michiganaerospace/Eco-Kit/weather ui mac/humidity.png

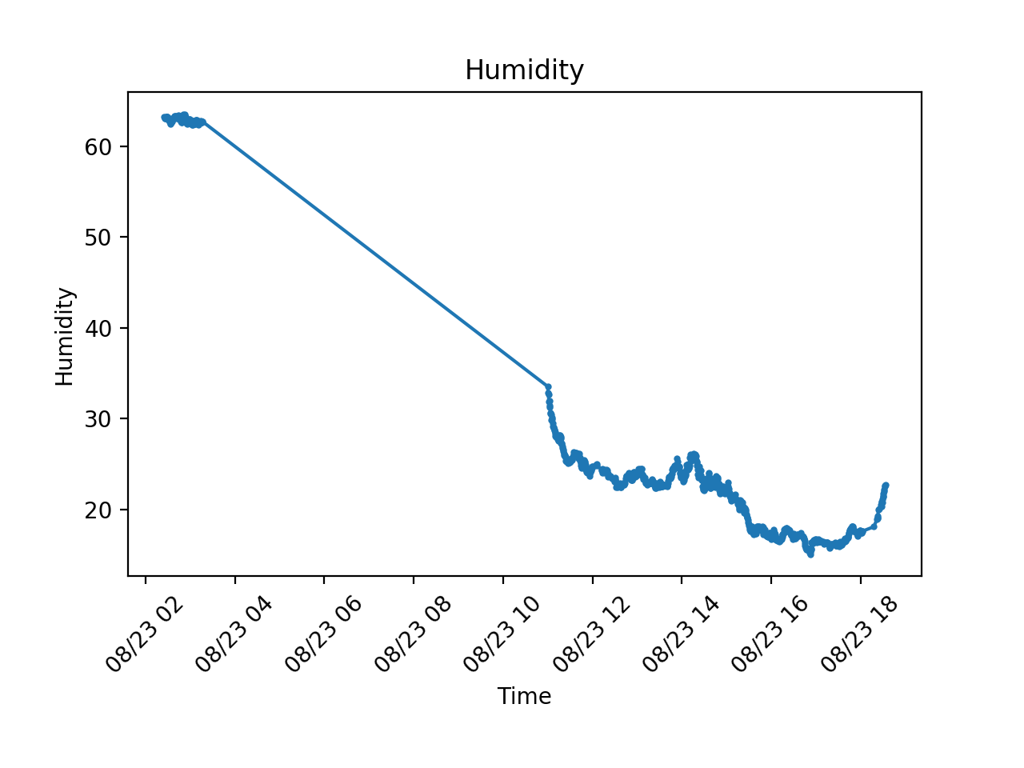
weather ui mac/humidity.png
