michiganaerospace/Eco-Kit/weather ui mac/no data.png

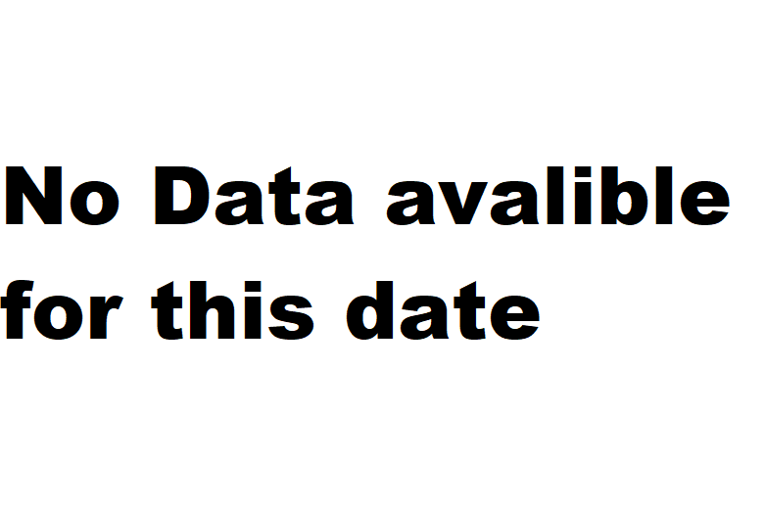
weather ui mac/no data.png
