michiganaerospace/Eco-Kit/weather ui mac/pressure.png

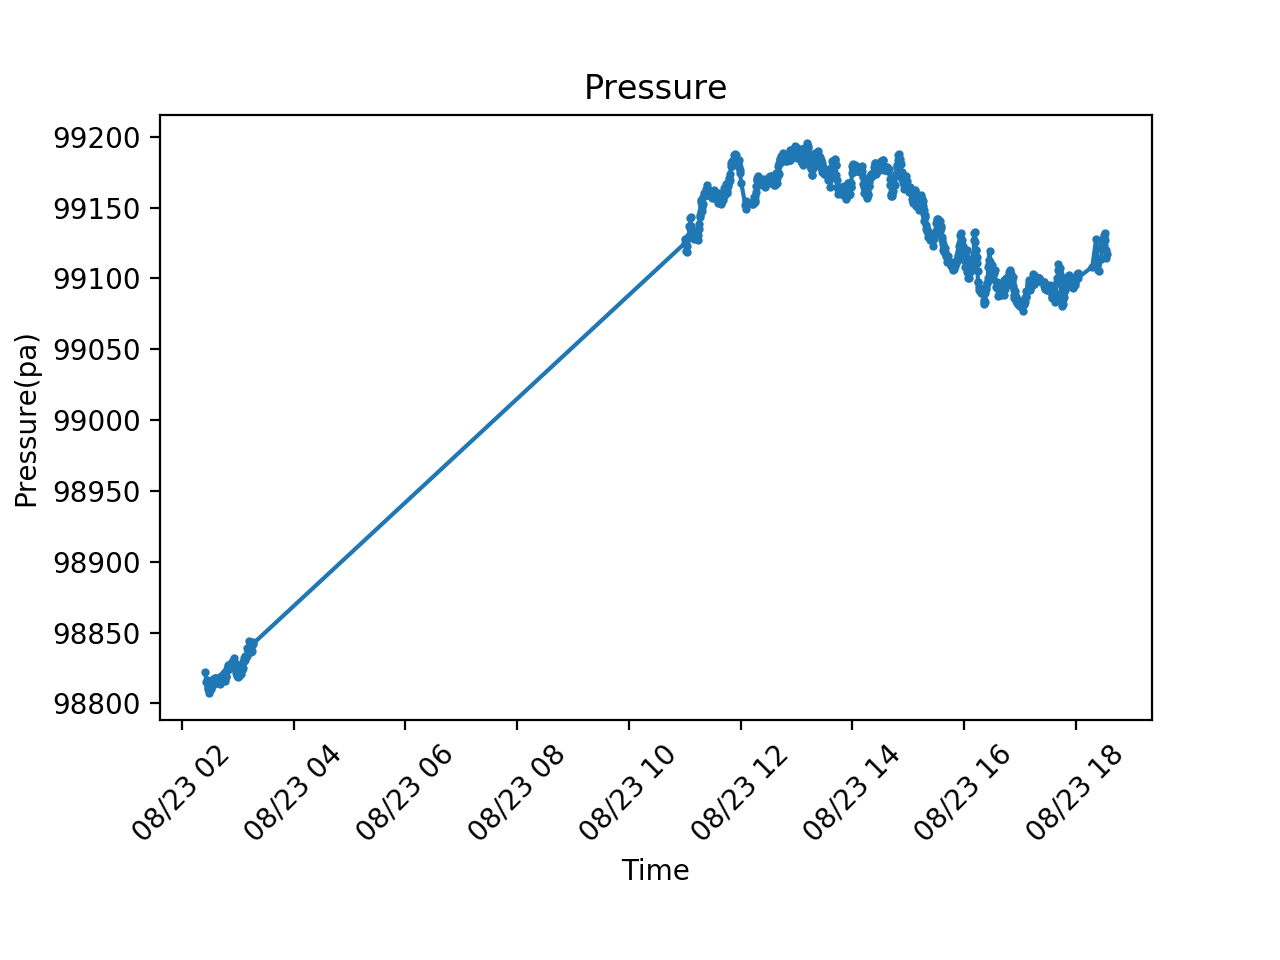
weather ui mac/pressure.png
