michiganaerospace/Eco-Kit/weather ui mac/temp.png

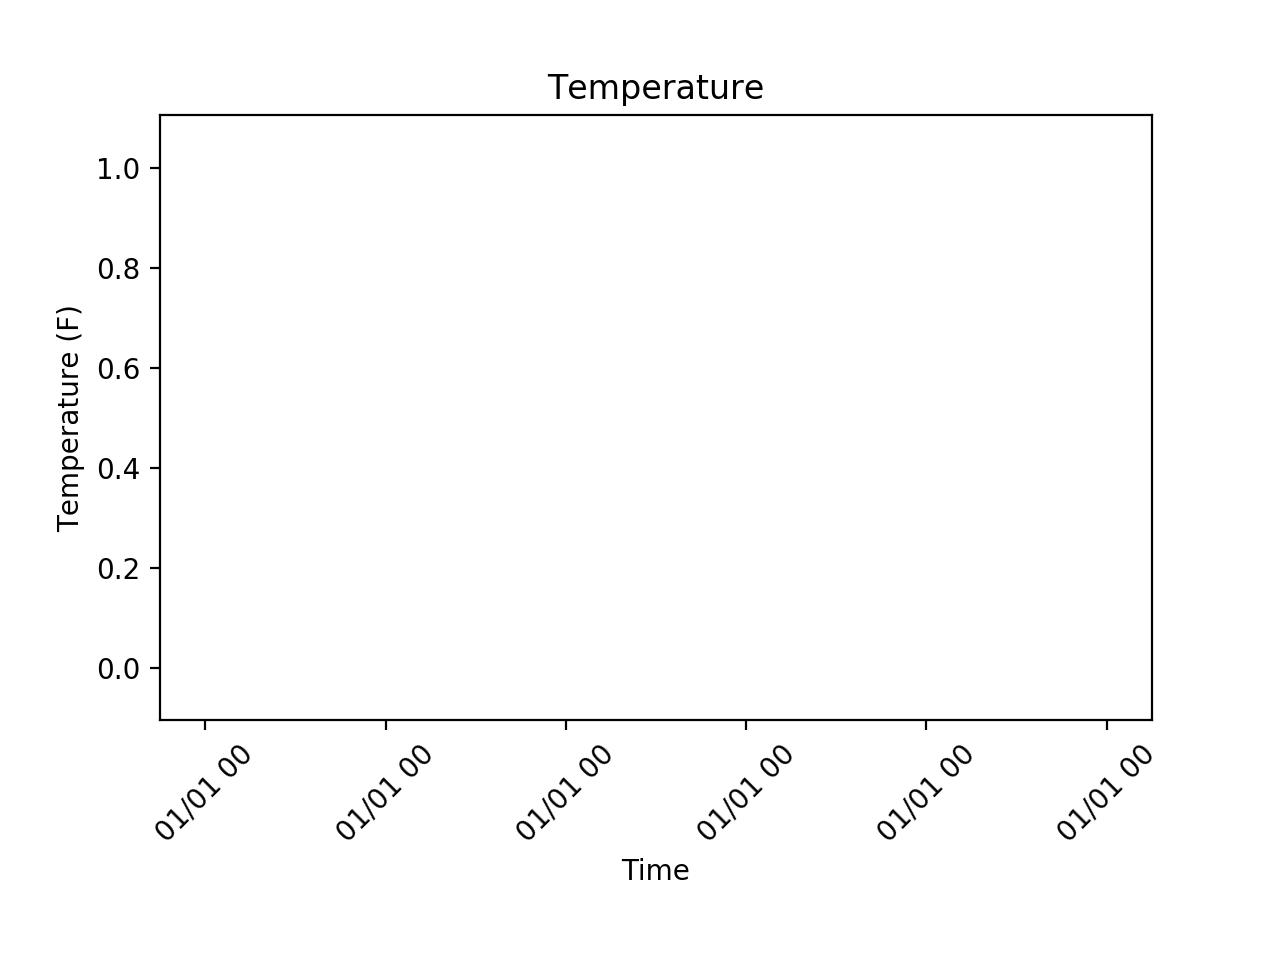
weather ui mac/temp.png
