michiganaerospace/Eco-Kit/weather ui mac/voltage.png

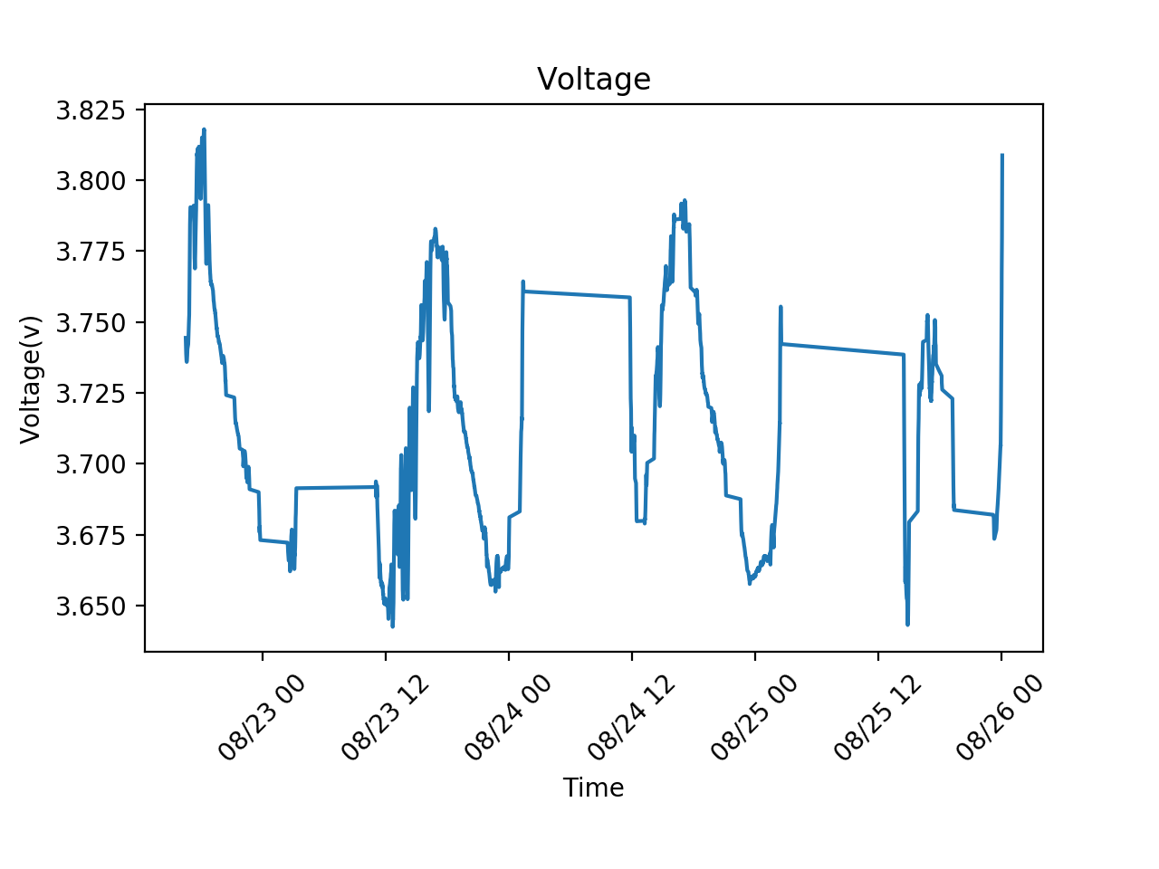
weather ui mac/voltage.png
