michiganaerospace/Eco-Kit/weather ui windows/app_data/temp.png

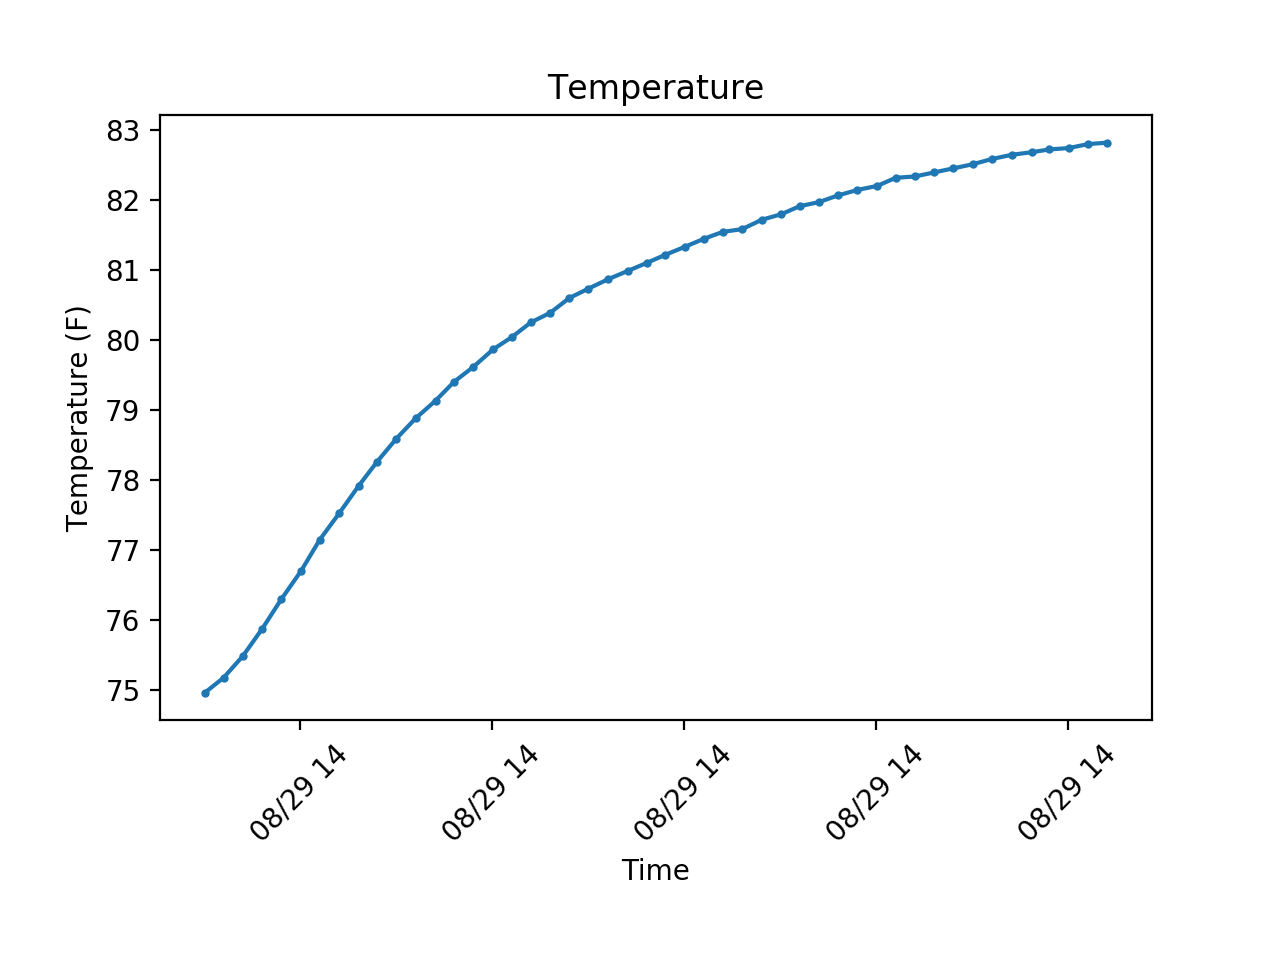
weather ui windows/app_data/temp.png
